triwaca/openDecabot/images/3dprinted_openDecabotMini.jpg

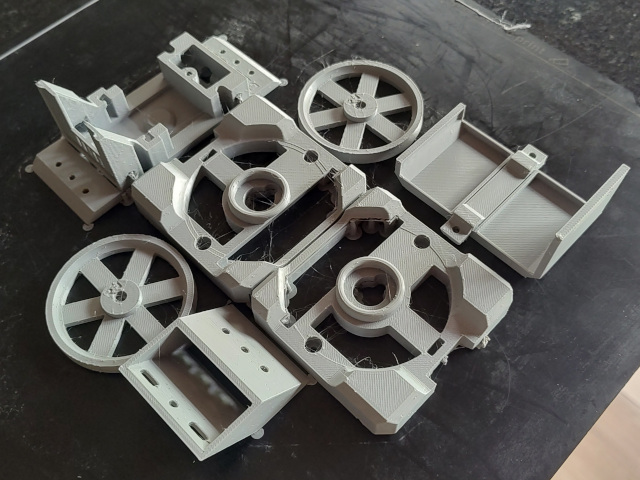
images/3dprinted_openDecabotMini.jpg
