triwaca/openDecabot/images/bottom3D.png

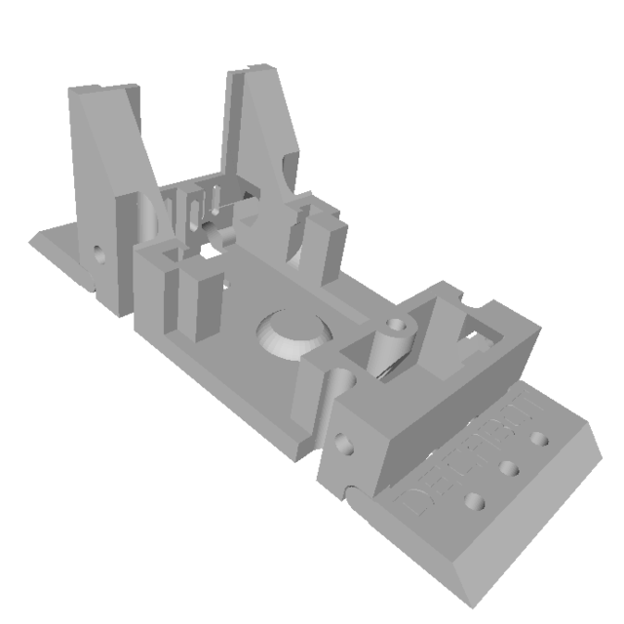
images/bottom3D.png
