triwaca/openDecabot/images/left3D.png

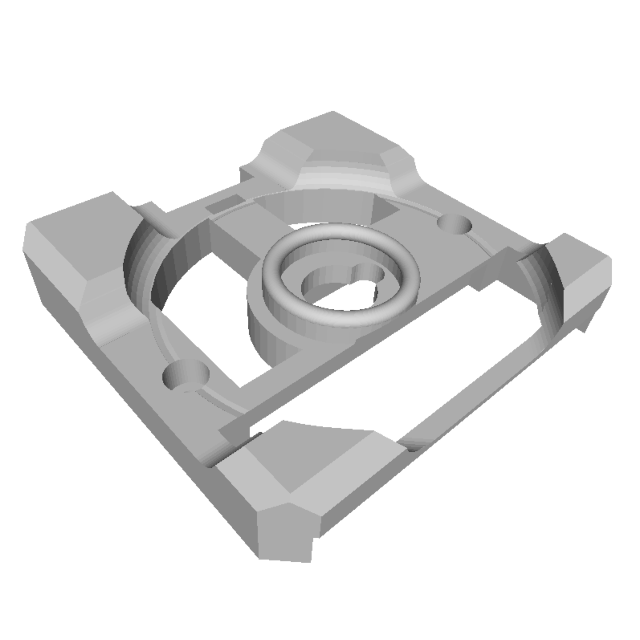
images/left3D.png
