triwaca/openDecabot/images/linef3D.png

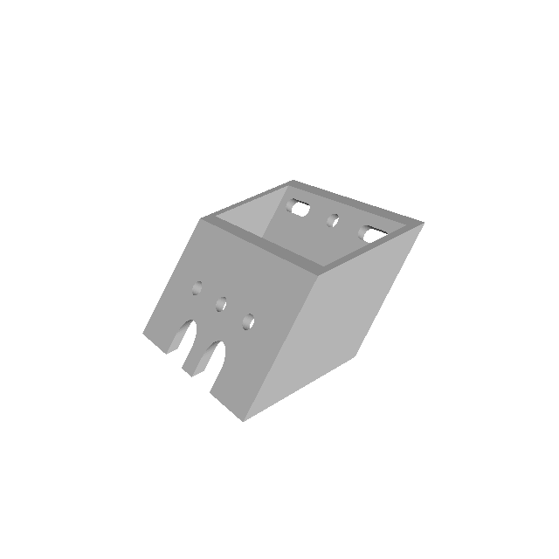
images/linef3D.png
