triwaca/openDecabot/images/miniShield_1.JPG

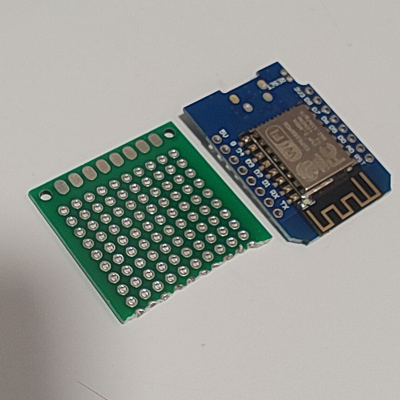
images/miniShield_1.JPG
