triwaca/openDecabot/images/miniShield_2.JPG

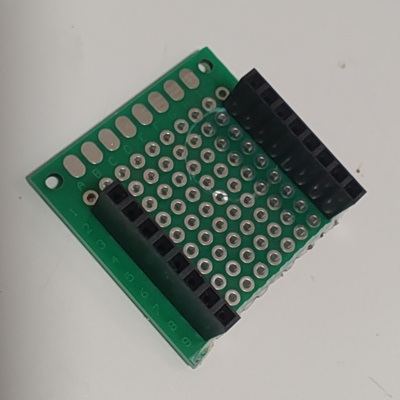
images/miniShield_2.JPG
