triwaca/openDecabot/images/miniShield_3.JPG

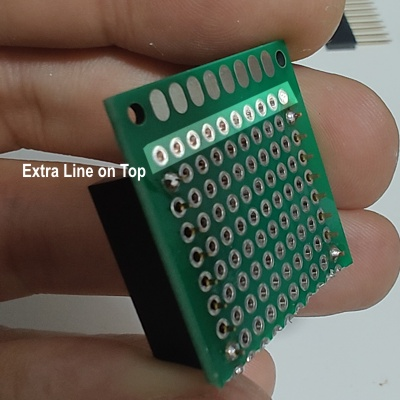
images/miniShield_3.JPG
