triwaca/openDecabot/images/miniShield_4.JPG

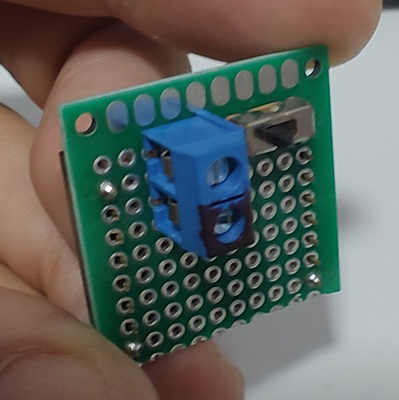
images/miniShield_4.JPG
