triwaca/openDecabot/images/miniShield_5.JPG

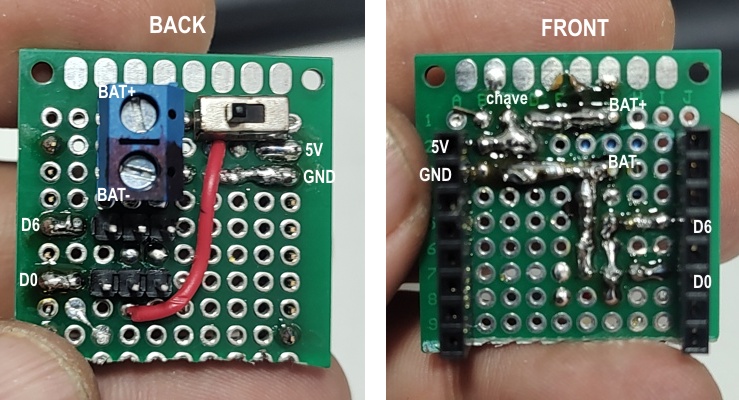
images/miniShield_5.JPG
