triwaca/openDecabot/images/miniShield_6.JPG

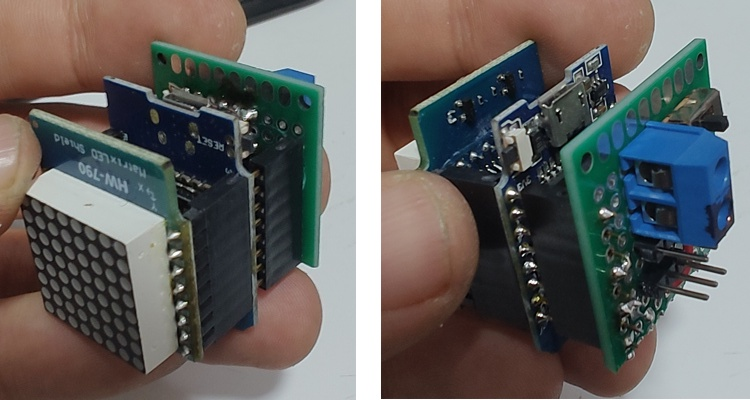
images/miniShield_6.JPG
