triwaca/openDecabot/images/miniShield_7.JPG

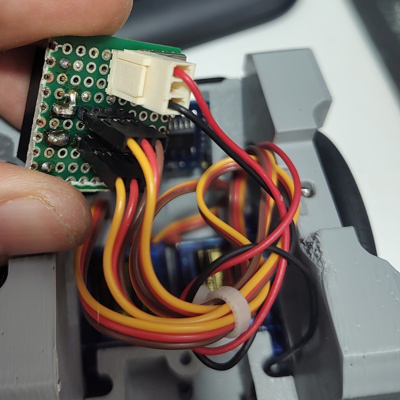
images/miniShield_7.JPG
