triwaca/openDecabot/images/right3D.png

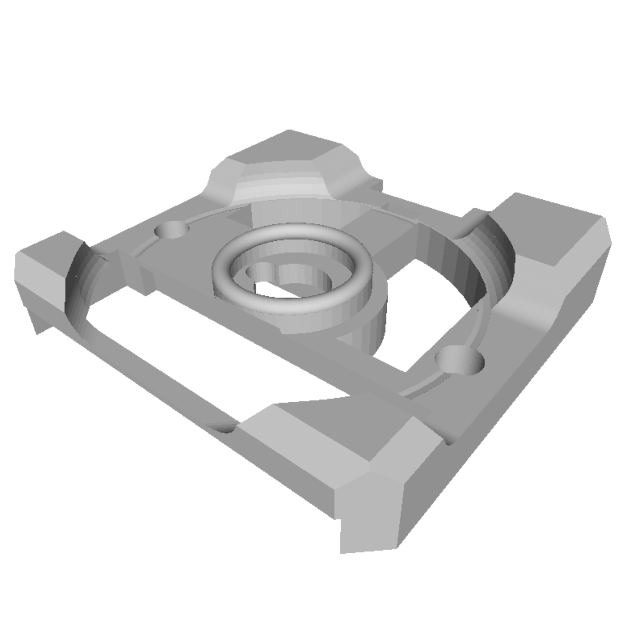
images/right3D.png
