triwaca/openDecabot/images/top3D.png

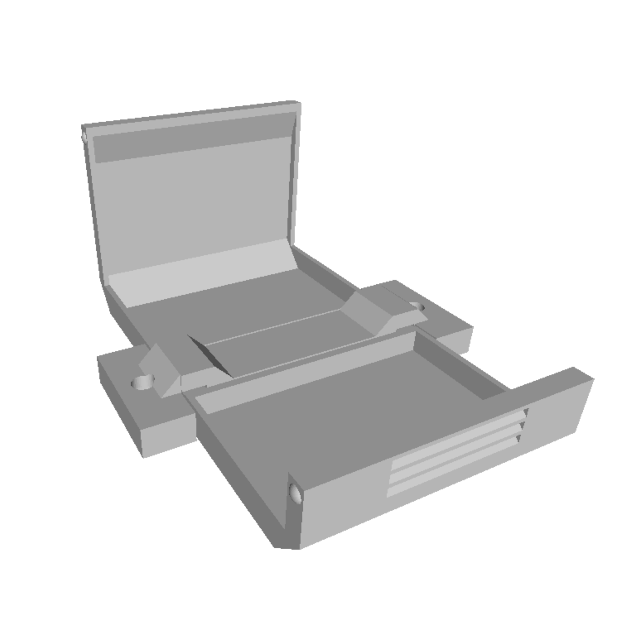
images/top3D.png
