triwaca/openDecabot/images/webReomte.jpg

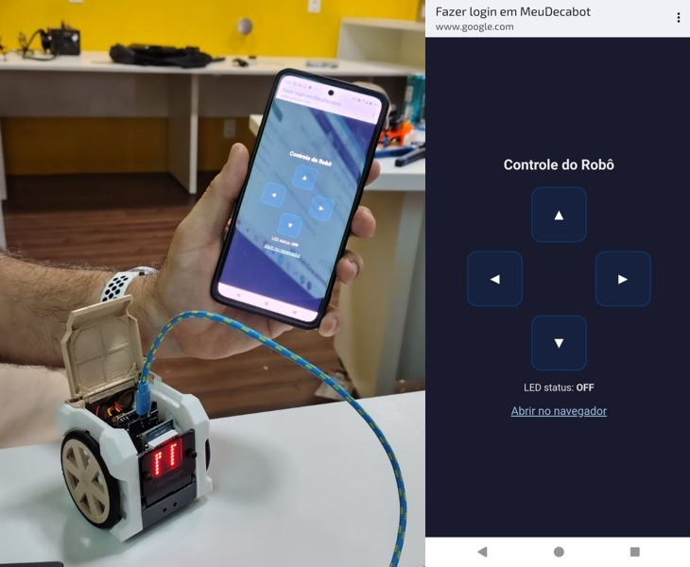
images/webReomte.jpg
