triwaca/openDecabot/images/wheel3D.png

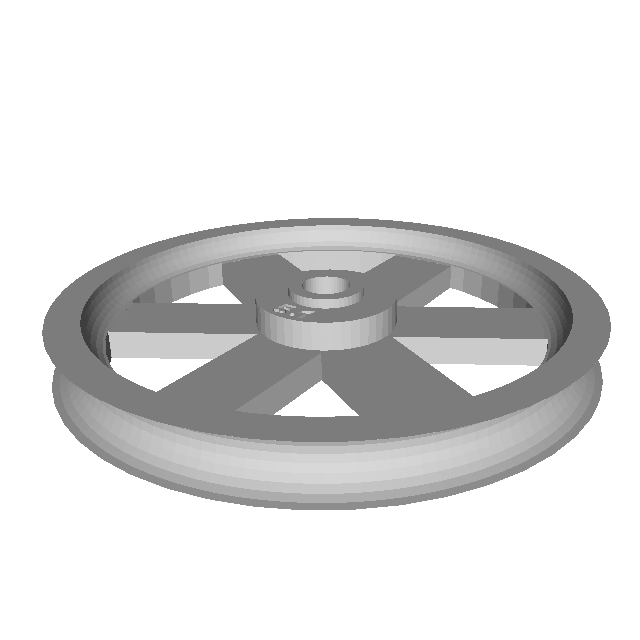
images/wheel3D.png
