triwaca/openDecabot/images/componentsWemos_ledMatrix.JPG

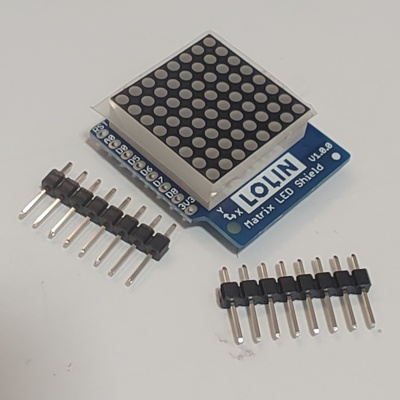
images/componentsWemos_ledMatrix.JPG
