triwaca/openDecabot/images/componentsWemos_ledMatrixConnected.JPG

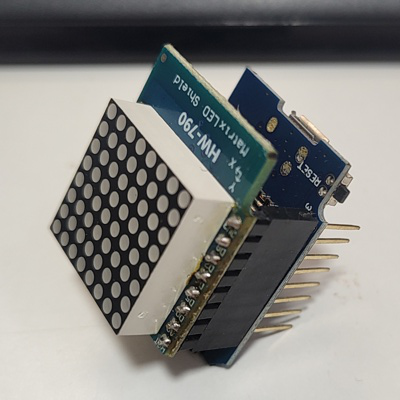
images/componentsWemos_ledMatrixConnected.JPG
