triwaca/openDecabot/images/componentsWemos_wemosD1Mini.JPG

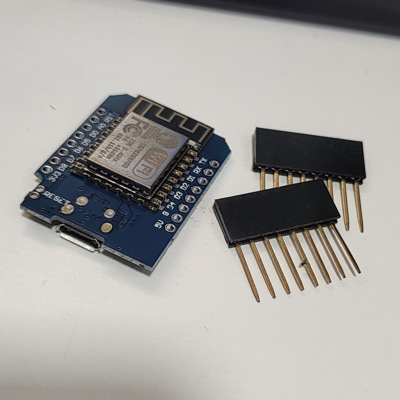
images/componentsWemos_wemosD1Mini.JPG
