triwaca/openDecabot/images/componentsWemos_ledMatrixAssembled.jpg

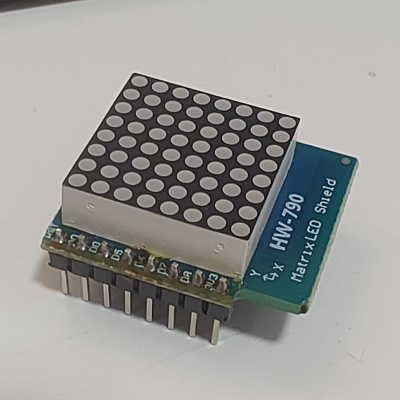
images/componentsWemos_ledMatrixAssembled.jpg
