triwaca/openDecabot/images/componentsWemos_wemosD1MiniSoldering.jpeg

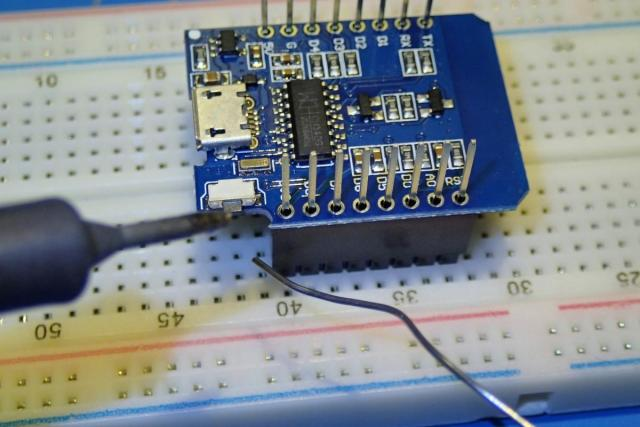
images/componentsWemos_wemosD1MiniSoldering.jpeg
