triwaca/openDecabot/images/montagemOpenDecabot_1.png

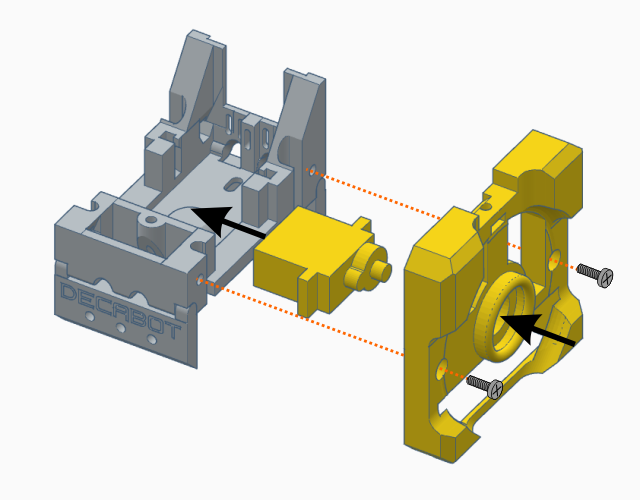
images/montagemOpenDecabot_1.png
