triwaca/openDecabot/images/montagemOpenDecabot_2.PNG

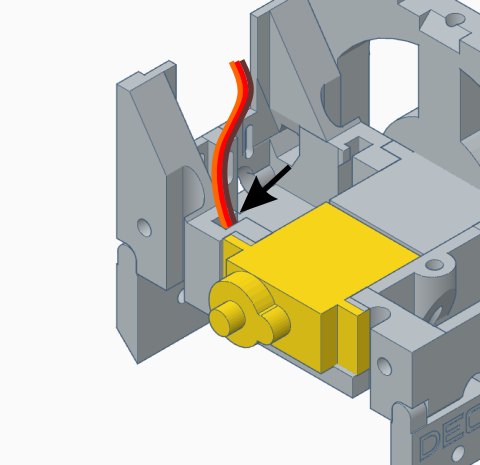
images/montagemOpenDecabot_2.PNG
