triwaca/openDecabot/images/montagemOpenDecabot_3.PNG

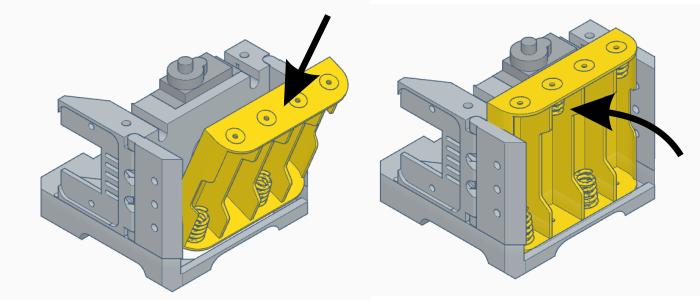
images/montagemOpenDecabot_3.PNG
