triwaca/openDecabot/images/montagemOpenDecabot_4.PNG

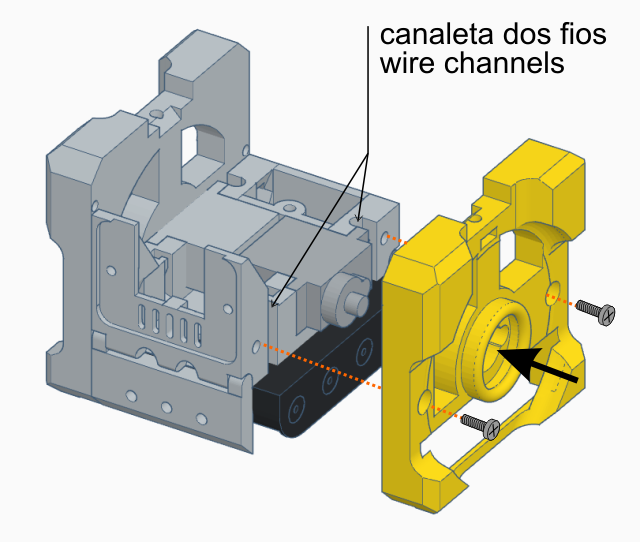
images/montagemOpenDecabot_4.PNG
