triwaca/openDecabot/images/montagemOpenDecabot_5.PNG

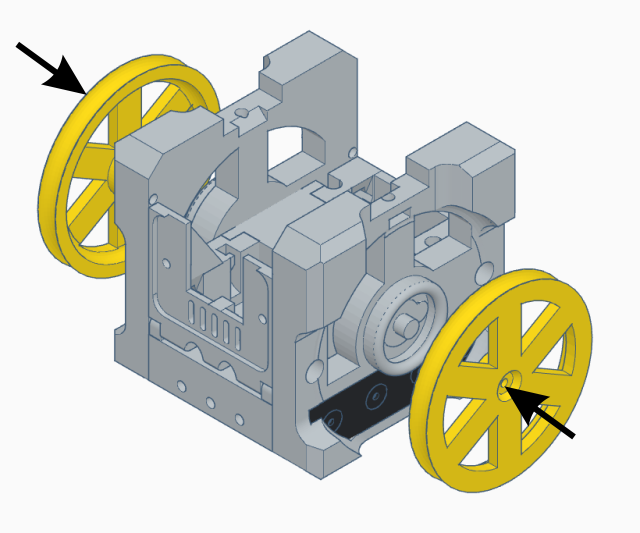
images/montagemOpenDecabot_5.PNG
