triwaca/openDecabot/images/montagemOpenDecabot_6.PNG

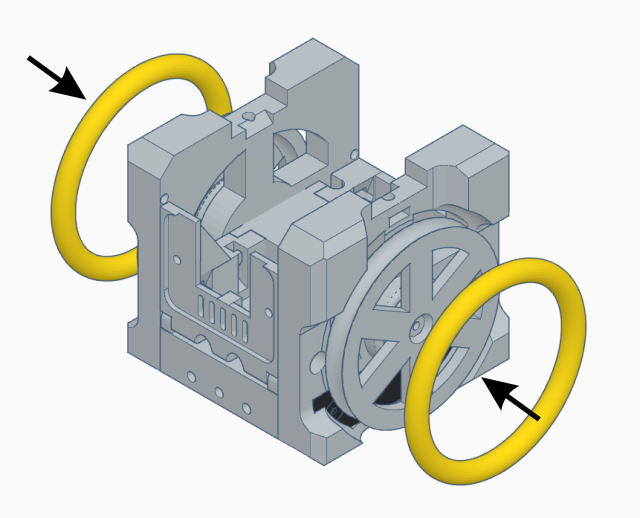
images/montagemOpenDecabot_6.PNG
