triwaca/openDecabot/images/montagemOpenDecabot_7.PNG

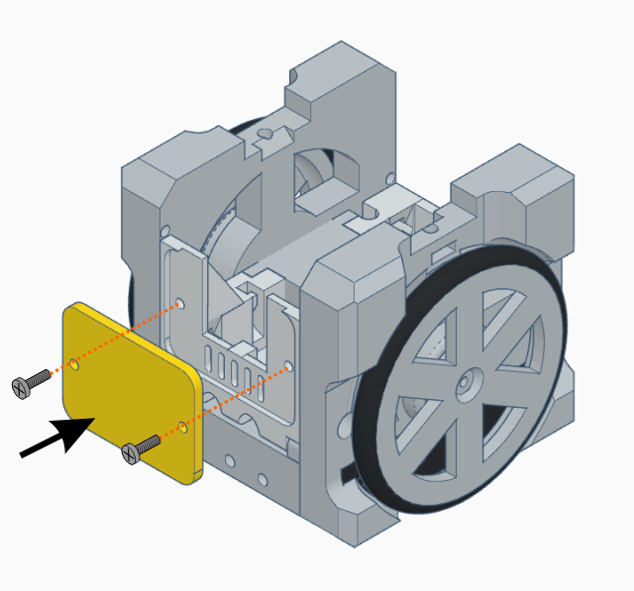
images/montagemOpenDecabot_7.PNG
