triwaca/openDecabot/images/montagemOpenDecabot_8.PNG

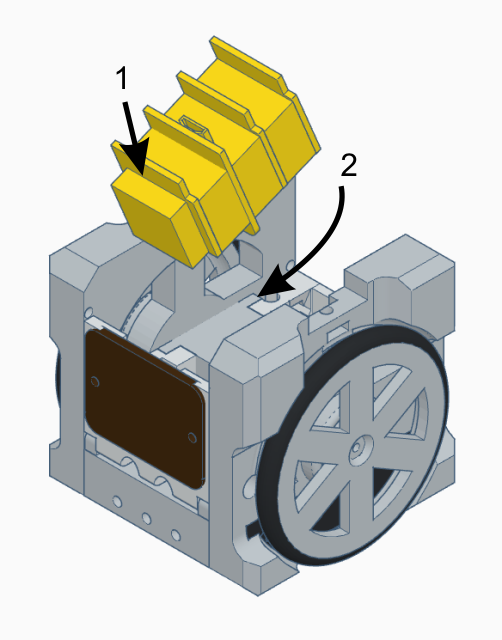
images/montagemOpenDecabot_8.PNG
