triwaca/openDecabot/images/montagemOpenDecabot_9.PNG

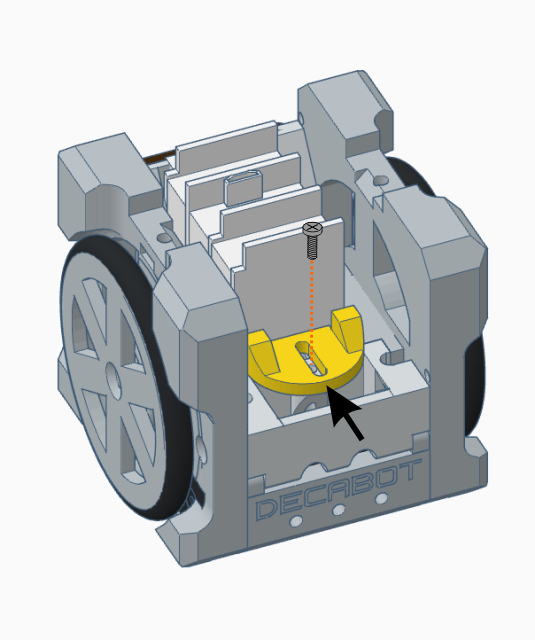
images/montagemOpenDecabot_9.PNG
