triwaca/openDecabot/images/montagemOpenDecabot_A.PNG

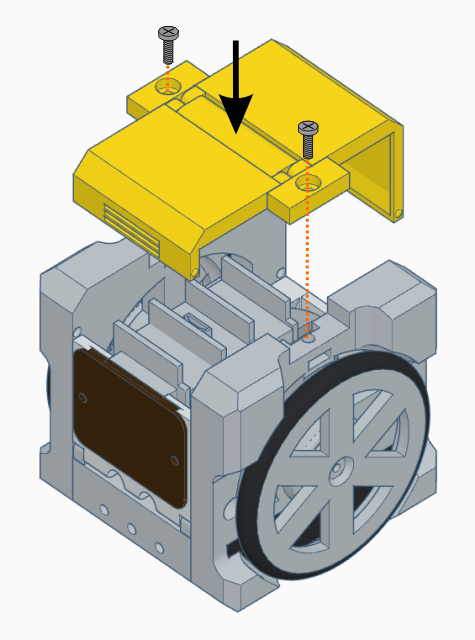
images/montagemOpenDecabot_A.PNG
