triwaca/openDecabot/ArduinoSketch/decabot_webControler/Possíveis Calibrações/decabot_webControler__1_/decabot_webControler__1_.ino

  /*
  * Captive Portal Decabot
  * Daniel Chagas, Nicole Akemi Takeda, Cauan Oliveira, Paulo Roberto Gomes
  *
  * Robô cria uma rede wifi com captive portal que exibe botões de controle
  * remoto que controlam os servo motores ligados às portas D0 (motor direito)
  * e D6 (motor esquerdo). 
  *
  * To use:
  * - Access the Wi-Fi network 'MeuDecabot' with a device such as smartphone,
  *   tablet or computer, and click on the login message. 
  * - You must see a page with a title and buttons who can control the movement
  * 
  * Hardware:
  * Wemos D1 Mini - https://www.wemos.cc/en/latest/d1/index.html
  * Matrix Led Shield - https://github.com/wemos/WEMOS_Matrix_LED_Shield_Arduino_Library
  * Decabot Mini Shield
  * 
  * PORTS                             _____________
  *                                  /             \
  *                             RST |*  ---------  *| TX 
  *           battery ---------- A0 |* |         | *| RX
  *         SERVO esq --GPIO16-- D0 |* |  ESP    | *| D1 ---I2C--- SCL
  *    led matrix CLK ---------- D5 |* |  8266   | *| D2 ---I2C--- SDA
  *         SERVO dir --GPIO12 - D6 |* |         | *| D3 --GPIO0-- SERVO
  *    led matrix DIN ---------- D7 |* |         | *| D4 --GPIO2
  *            buzzer --GPIO15-- D8 |*  ---------  *| GND
  *                             3V3 |*             *| 5V
  *                                  \              |
  *                            reset  |      D1mini |
  *                                    \___________/
  */


  #include <ESP8266WiFi.h>
  #include <ESPAsyncTCP.h>        //tested on 1.2.4 from https://github.com/dvarrel/ESPAsyncTCP
  #include <ESPAsyncWebServer.h>  //tested on https://github.com/lacamera/ESPAsyncWebServer
  #include <DNSServer.h>
  #include <Servo.h>
  #include <Adafruit_GFX.h>       // tested on 1.11.10
  #include <WEMOS_Matrix_GFX.h>   // tested on 1.4.0iu332
  #define buzzer D8

  MLED matrix(7);

  int slowSpeed = 40; //number between 1 and 180 max.
  int fastSpeed = 60; //number between 1 and 180 max.

  int calibration = 0; //number between -50 and 50 to balance motors

  int lpos = 1;
  int rpos = 6; 
  int aleat = 5;

  bool awake = false;

  String serialAtual = "";

  const char *ssid = "MeuDecabot";
  const char *password = "";
  Servo servo0;
  Servo servo6;


  const int decabotMusic[4][3]{ { 494, 2, 3 }, { 554, 2, 4 }, { 440, 2, 5 }, { 880, 1, 6 } };
  static const uint8_t PROGMEM decabotLogo[4][5] = {{0b11001110,0b10101000,0b10101100,0b10101000,0b11001110},{0b00110010,0b01000101,0b01000111,0b01000101,0b00110101},{0b11000100,0b10101010,0b11001010,0b10101010,0b11000100},{0b01110100,0b00100100,0b00100100,0b00100000,0b00100100}};


  DNSServer dnsServer;
  const byte DNS_PORT = 53;

  AsyncWebServer server(80);

  const int LED_PIN = LED_BUILTIN;
  bool ledState = false;

  void notFound(AsyncWebServerRequest *request) {
    request->redirect("/");
  }

  int neutralLeft  = 93;
  int neutralRight = 93;

  void printWeb(String texto) {
    serialAtual = texto;
  }

  void motorLeft(int pot) {
    if (pot == 0) {
      servo0.write(neutralLeft);
    } else {
      int vel = neutralLeft + map(pot, -100, 100, fastSpeed, -fastSpeed);
      servo0.write(vel);
    }
  }

  void motorRight(int pot) {
    if (pot == 0) {
      servo6.write(neutralRight);
    } else {
      int vel = neutralRight - map(pot, -100, 100, fastSpeed, -fastSpeed);
      servo6.write(vel);
    }
  }

  void setup() {
    Serial.begin(115200);
    Serial.println();
    Serial.println();
    Serial.println("Decabot");
    pinMode(buzzer, OUTPUT);
    matrix.setRotation(2);
    servo0.attach(D0);
    servo6.attach(D6);
    Serial.begin(115200);

    pinMode(LED_PIN, OUTPUT);
    digitalWrite(LED_PIN, HIGH); // LED off (ativo em LOW)
    ledState = false;

    WiFi.mode(WIFI_AP);
    WiFi.softAP(ssid, password);
    IPAddress myIP = WiFi.softAPIP();
    Serial.print("AP IP address: ");
    Serial.println(myIP);

    dnsServer.start(DNS_PORT, "*", myIP);

    // Página raiz (cativa)
    server.on("/", HTTP_GET, [myIP](AsyncWebServerRequest *request) {
      String ipStr = myIP.toString();
      String html = R"rawliteral(
  <!DOCTYPE html>
  <html lang="pt-BR">
  <head>
    <meta charset="UTF-8" />
    <meta name="viewport" content="width=device-width, initial-scale=1" />
    <title>Controle do Robô</title>
    <style>
      :root{
        --bg:#1a1a2e;
        --btn:#16213e;
        --border:#0f3460;
        --txt:#fff;
        --accent:#0f3460;
      }
      *{box-sizing:border-box}
      html,body{
        height:100%;
        margin:0;
      }
      body {
        background: var(--bg);
        font-family: Arial, Helvetica, sans-serif;
        color: var(--txt);
        display: flex;
        flex-direction: column;
        justify-content: center;
        align-items: center;
        gap: 18px;
        user-select: none;
        -webkit-user-select: none;
      }

      .calibrador {
        text-align: center;
        margin-top: 10px;
      }

      h1{margin:0 0 4px 0;font-size:20px;opacity:.9}
      .controle {
        display: grid;
        grid-template-columns: 90px 90px 90px;
        grid-template-rows: 90px 90px 90px;
        gap: 14px;
        touch-action: none; /* evita scroll durante o toque */
      }
      .controle.dormindo button:not(.state1):not(.state2):not(.dbButton) {
        background: #2a2a2a;
        border-color: #444444;
        color: #888888;
        transition: background .3s, border-color .3s, color .3s;
        pointer-events: none;
      }
      button {
        background: var(--btn);
        color: var(--txt);
        border: 2px solid var(--border);
        border-radius: 16px;
        font-size: 22px;
        cursor: pointer;
        transition: transform .08s ease, background .15s ease;
        outline: none;
        -webkit-tap-highlight-color: transparent;
      }
      button:active{
        transform: scale(0.97);
        background: var(--accent);
      }
      /* posição dos botões */
      .frente  { grid-column: 2; grid-row: 1; }
      .esquerda{ grid-column: 1; grid-row: 2; }
      .state1  { grid-column: 2; grid-row: 2; }
      .state2  { grid-column: 2; grid-row: 2; }
      .direita { grid-column: 3; grid-row: 2; }
      .tras    { grid-column: 2; grid-row: 3; }
      .dbButton{ grid-column: 3; grid-row: 3; }

      .status{
        font-size:14px;
        opacity:.85;
      }
      .dbPanel{
        background: var(--btn);
        color: var(--txt);
        border: 2px solid rgb(255, 235, 205);
        overflow-y: scroll;
        border-radius: 16px;
        font-size: 16px;
        box-shadow: rgba(0, 0, 0, 0.342) 5px 5px 10px;
        width: 250px;
        height: 200px;
      }

      @media (max-width: 420px){
        .controle{
          grid-template-columns: 80px 80px 80px;
          grid-template-rows: 80px 80px 80px;
          gap: 12px;
        }
      }
    </style>
  </head>
  <body>
    <h1>Controle do Robô</h1>

    <div class="controle">
      <button class="frente"   aria-label="Frente"   onpointerdown="press('Front')" onpointerup="release()" onpointerleave="release()">▲</button>
      <button class="esquerda" aria-label="Esquerda" onpointerdown="press('Left')"  onpointerup="release()" onpointerleave="release()">◄</button>
      <button class="direita"  aria-label="Direita"  onpointerdown="press('Right')" onpointerup="release()" onpointerleave="release()">►</button>
      <button class="tras"     aria-label="Trás"     onpointerdown="press('Back')"  onpointerup="release()" onpointerleave="release()">▼</button>
      <button class="state1"    aria-label="Estado"  onclick="acordar('levanta')">🌜</button>
      <button class="state2"    aria-label="Estado"  onclick="acordar('apaga')">🌞</button>
      <button class="dbButton"  aria-label="debugar" onclick="debugar()">DB</button>
    </div>

    <div class="calibrador">
      <span>Calibração: <strong id="valorCalib" class="valorCalib">0</strong></span>
      <br>
      <input id="calibBarra" type="range"  min="-50" max="50" value="0" onchange="newCalibration(this.value)" oninput="changeCVT(this.value)">
    </div>

    <div class="status">LED status: <strong id="ledState">unknown</strong></div>
    <a href="http://)rawliteral" + ipStr + R"rawliteral(/" style="color:#9bd">Abrir no navegador</a>
    <div class="dbPanel">
      <ul class="serials"></ul>
    </div>
    <script>
      let dbOn = false;
      let isPressed = false;
      let acordado = false;
      let intervalo = null;
      const controle = document.querySelector('.controle');
      const botaoDormindo = document.querySelector('.state1');
      const botaoAcordado = document.querySelector('.state2');
      const dbPanel = document.querySelector('.dbPanel');
      const serials = document.querySelector('.serials');
      dbPanel.style.visibility = "hidden";
      botaoAcordado.style.visibility = "hidden";
      controle.classList.add('dormindo');

      function changeCVT(value) {
        const textCalib = document.getElementById('valorCalib');
        textCalib.innerHTML = value;
      }

      function newCalibration(value) {
        return fetch('/calibrar?val=' + value)
          .catch(() => {});
      }

      function setLED(state) {
        return fetch('/led?state=' + state)
          .then(r => r.text())
          .then(text => {
            const el = document.getElementById('ledState');
            if (el) el.textContent = text;
          })
          .catch(() => {});
      }

      function press(direction){
        if (isPressed) return;
        isPressed = true;
        setLED(direction);
      }

      function release(){
        if (!isPressed) return;
        isPressed = false;
        setLED('Stop'); // volta para neutro ao SOLTAR
      }

      function acordar(estado) {
        if (!acordado) {
          acordado = true;
          botaoAcordado.style.visibility = "visible";
          botaoDormindo.style.visibility = "hidden";
          controle.classList.remove('dormindo');
          return fetch('/acordar?situacao=' + estado)
          .catch(() => {});
        }else {
          acordado = false;
          botaoAcordado.style.visibility = "hidden";
          botaoDormindo.style.visibility = "visible";
          controle.classList.add('dormindo');
          return fetch('/acordar?situacao=' + estado)
          .catch(() => {});
        }
      }

      function debugar() {
        if (!dbOn) {
          dbOn = true;
          dbPanel.style.visibility = "visible";
          intervalo = setInterval(() => {
            fetch('/serial')
            .then(r => r.text())
            .then(text => {
              if (text != "") {
                const newItem = document.createElement('li');
                newItem.innerHTML = `${text}`;
                serials.appendChild(newItem);
              }
            })
          }, 500);
        }else {
          dbOn = false;
          dbPanel.style.visibility = "hidden";
          clearInterval(intervalo);
          intervalo = null;
        }
      }

      function getLEDStatus() {
        fetch('/status')
          .then(r => r.text())
          .then(text => {
            const el = document.getElementById('ledState');
            if (el) el.textContent = text;
          })
          .catch(() => {});
      }

      // Se sair da aba, solta os botões
      window.addEventListener('blur', release);
      // Estado inicial
      window.onload = getLEDStatus;
    </script>
  </body>
  </html>
      )rawliteral";

      request->send(200, "text/html", html);
    });

    // Prints no painel de Debug
    server.on("/serial", HTTP_GET, [](AsyncWebServerRequest *request) {
      request->send(200, "text/plain", serialAtual);
      serialAtual = "";
    });

    // Comandos: Front / Left / Right / Back / Stop
    server.on("/led", HTTP_GET, [](AsyncWebServerRequest *request) {
      if (request->hasParam("state")) {
        String state = request->getParam("state")->value();
        printWeb(state);

        if (state == "Front") {
          digitalWrite(LED_PIN, LOW);
          ledState = true;
          motorLeft(100);
          motorRight(100);
        } else if (state == "Left") {
          digitalWrite(LED_PIN, LOW);
          ledState = true;
          motorLeft(50);
          motorRight(-50);

        } else if (state == "Right") {
          digitalWrite(LED_PIN, LOW);
          ledState = true;
          motorLeft(-50);
          motorRight(50);

        } else if (state == "Back") {
          digitalWrite(LED_PIN, LOW);
          ledState = true;
          motorLeft(-50);
          motorRight(-50);

        } else if (state == "Stop") {
          digitalWrite(LED_PIN, HIGH);
          ledState = false;
          motorLeft(0);
          motorRight(0);

        } else {
          request->send(400, "text/plain", "Invalid state");
          return;
        }

        request->send(200, "text/plain", ledState ? "ON" : "OFF");
      } else {
        request->send(400, "text/plain", "Missing parameter");
      }
    });

    server.on("/status", HTTP_GET, [](AsyncWebServerRequest *request) {
      request->send(200, "text/plain", ledState ? "ON" : "OFF");
    });

    server.onNotFound(notFound);

    // Calibração do Decabot
    server.on("/calibrar", HTTP_GET, [](AsyncWebServerRequest *request) {
      if (request->hasParam("val")) {
          String valorString = request->getParam("val")->value();
          calibration = valorString.toInt();
          neutralLeft  = 90 + calibration;
          neutralRight = 90 - calibration;
          request->send(200, "text/plain", "Calibrado com sucesso!");
      } else {
          request->send(400, "text/plain", "Parâmetro ausente");
      }
  });
    
    //Acordar e dormir
    server.on("/acordar", HTTP_GET, [](AsyncWebServerRequest *request) {
      if (request->hasParam("situacao")) {
          String situString = request->getParam("situacao")->value();
          if(situString == "levanta"){
            awake = true;
            request->send(200, "text/plain", "Decabot acordado!");
          } else if(situString == "apaga"){
            awake = false;
            request->send(200, "text/plain", "Decabot dormindo!");
          } else {
            request->send(400, "text/plain", "Valor inválido");
          }
      }
    });
    
    server.begin();
    for (int i = 0; i < 4; i++) {
      matrix.clear();
      matrix.drawBitmap(0, 2, decabotLogo[i] , 8, 5, LED_ON);
      matrix.writeDisplay();
      tone(buzzer, decabotMusic[i][0], decabotMusic[i][1] * 200);
      delay(decabotMusic[i][1] * 200);
      noTone(buzzer);
    }
    delay(500);
    matrix.clear();
  }

  void loop() {
    dnsServer.processNextRequest();

    if(awake){
      // animação dos olhos + buzzer (mantida)
      matrix.clear();
      matrix.drawLine(lpos, 2, lpos, 7, LED_ON);
      matrix.drawLine(rpos, 2, rpos, 7, LED_ON);
      matrix.writeDisplay();
      delay(1000);

      // efeito de piscar
      for (int j = 0; j < random(3); j++) {
        for (int i = 2; i < 7; i++) {
          matrix.clear();
          matrix.drawLine(lpos, i, lpos, 7, LED_ON);
          matrix.drawLine(rpos, i, rpos, 7, LED_ON);
          matrix.writeDisplay();
          digitalWrite(buzzer, HIGH);
          delay(15);
          digitalWrite(buzzer, LOW);
          delay(15);
        }
        for (int i = 7; i > 2; i--) {
          matrix.clear();
          matrix.drawLine(lpos, i, lpos, 7, LED_ON);
          matrix.drawLine(rpos, i, rpos, 7, LED_ON);
          matrix.writeDisplay();
          digitalWrite(buzzer, HIGH);
          delay(15);
          digitalWrite(buzzer, LOW);
          delay(15);
        }
      }
    
      // olhar para os lados
      aleat = random(10);
      if (aleat < 2) {
        lpos = 0;
        rpos = 5;
      } else if (aleat > 7) {
        lpos = 2;
        rpos = 7;
        delay(15);
      } else {
        lpos = 1;
        rpos = 6;
        delay(15);
      }
    } else {
      matrix.clear();
      matrix.drawLine(0, 7, 2, 7, LED_ON);
      matrix.drawLine(5, 7, 7, 7, LED_ON);
      matrix.writeDisplay();
    }
  }
